kristinpaget/GuardBunny/DC25/GB_v2d6_layout.png

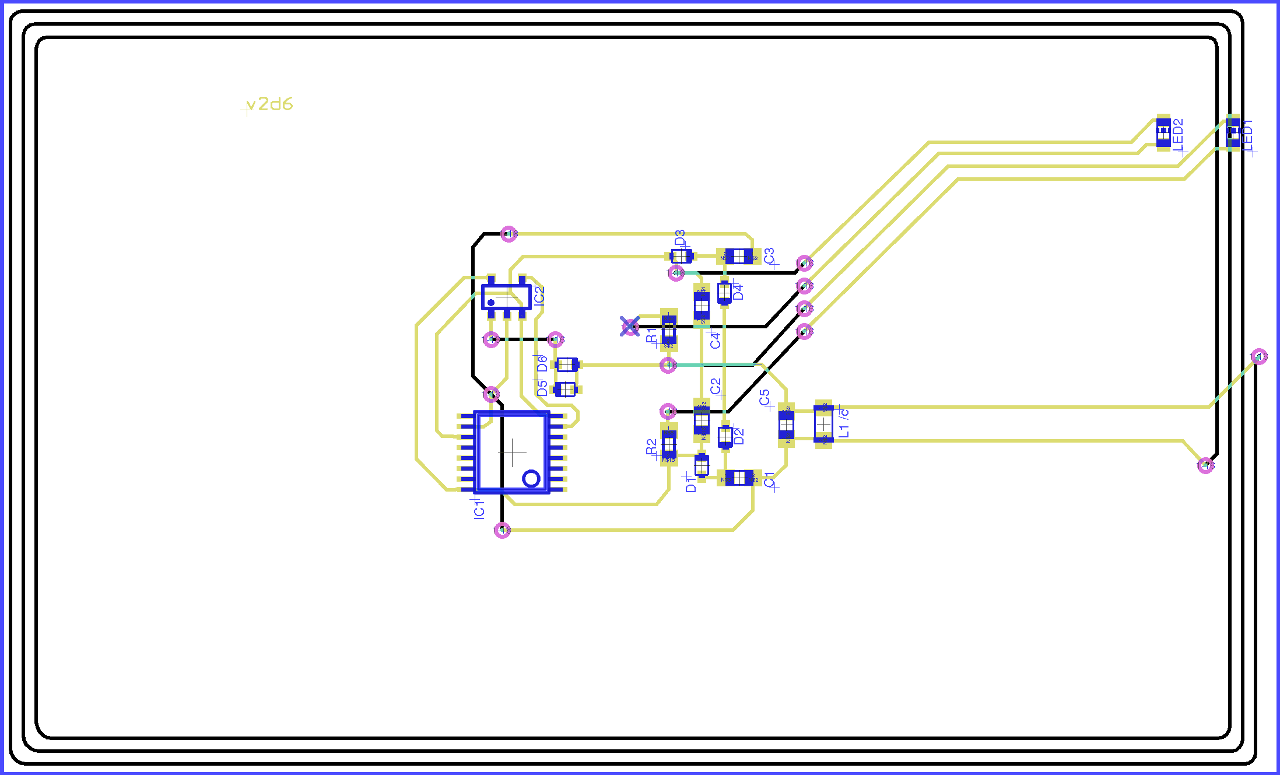
DC25/GB_v2d6_layout.png
